ruenahcmohr/FollowerRing/Circuit/p1270998.jpg

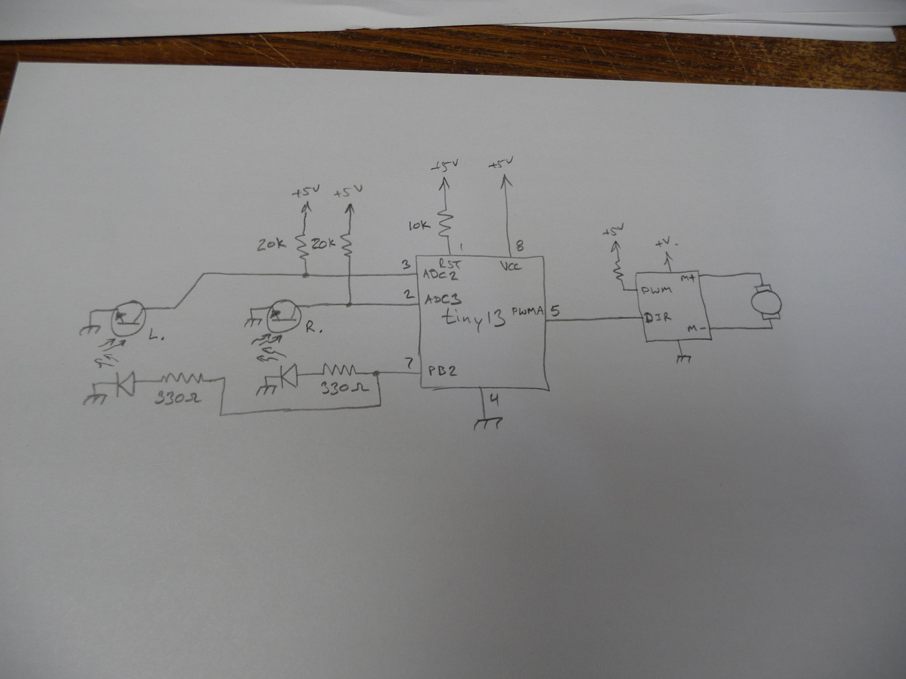
Circuit/p1270998.jpg
