ruenahcmohr/FollowerRing/p1270893.jpg

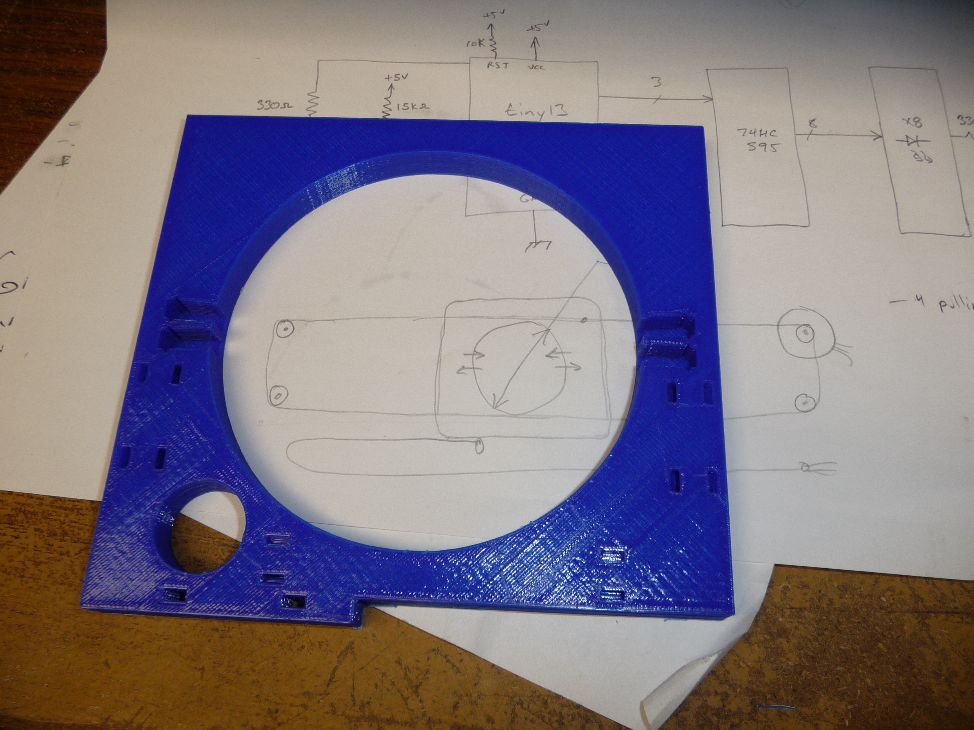
p1270893.jpg
