ruenahcmohr/FollowerRing/p1280001.jpg

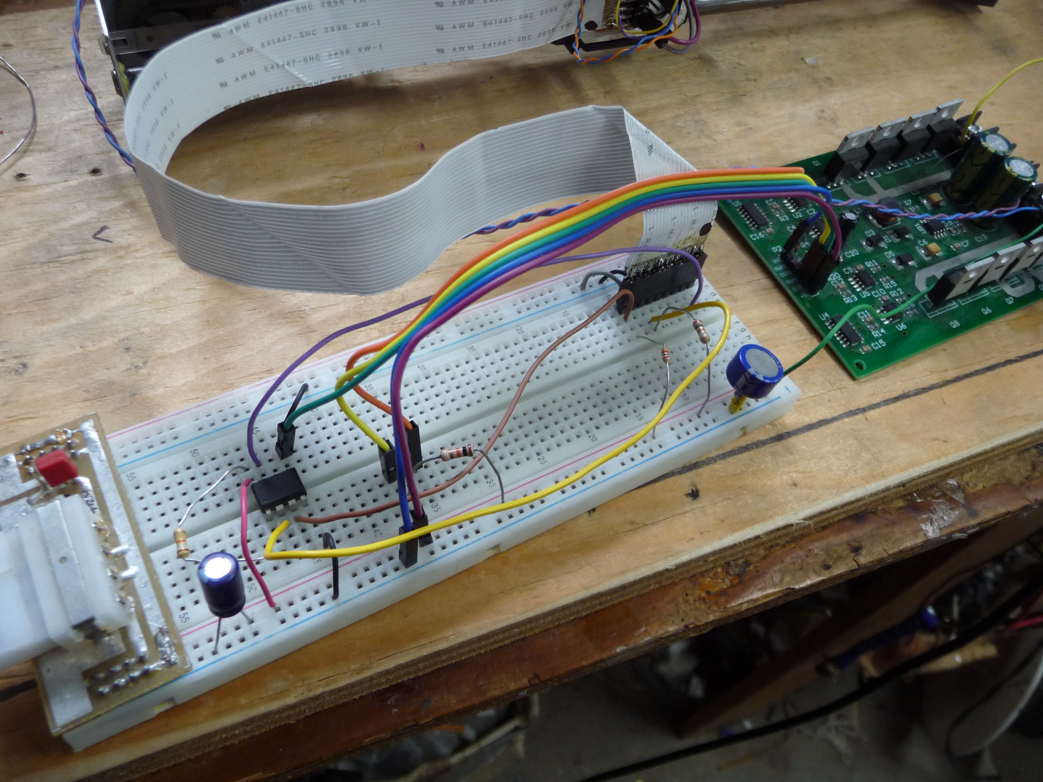
p1280001.jpg
