ruenahcmohr/FollowerRing/p1280002.jpg

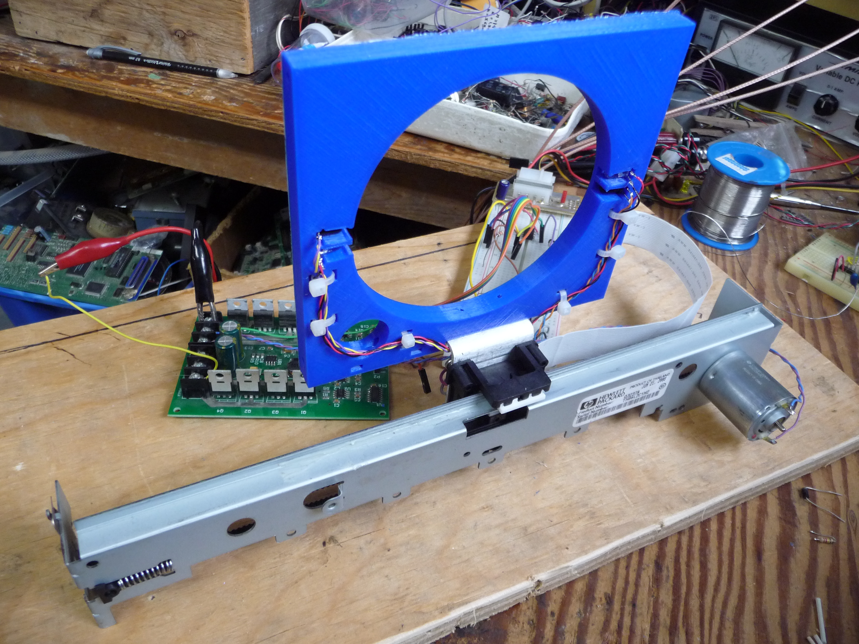
p1280002.jpg
