ruenahcmohr/FollowerRing/p1280003.jpg

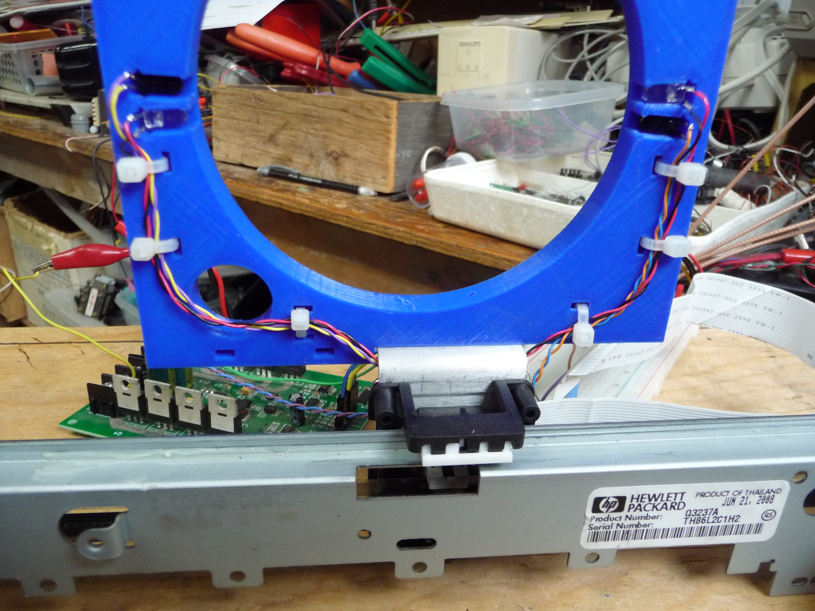
p1280003.jpg
