ruenahcmohr/FollowerRing/p1280004.jpg

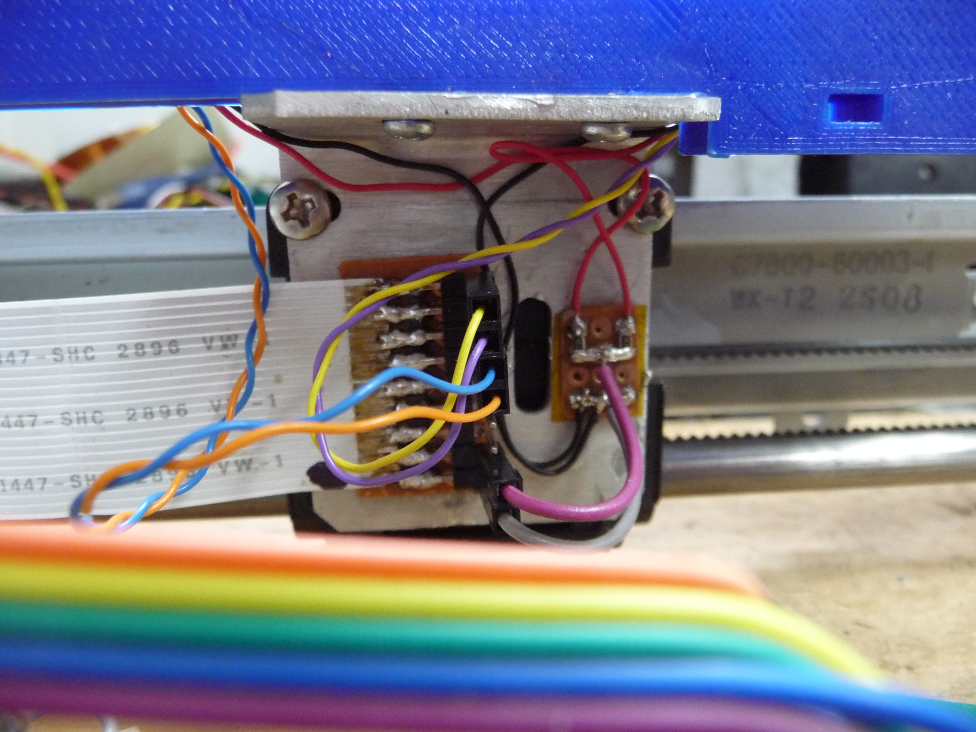
p1280004.jpg
